marrold/BBCWinchesterPro/images/HDINIT_8BIT.jpg

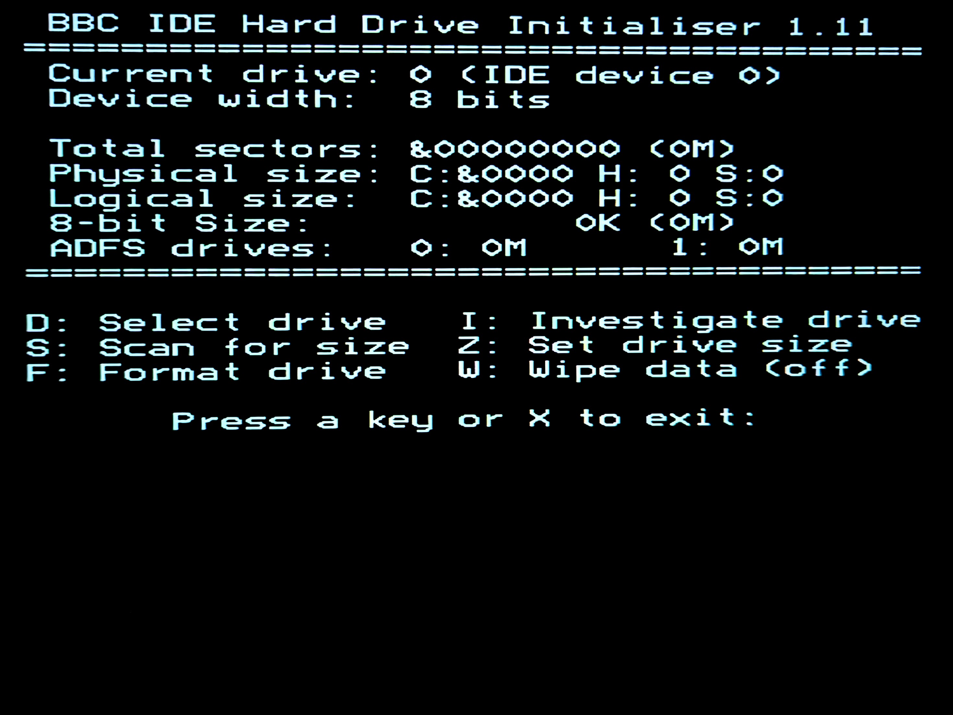
images/HDINIT_8BIT.jpg
