marrold/BBCWinchesterPro/images/HDINIT_FORMAT.jpg

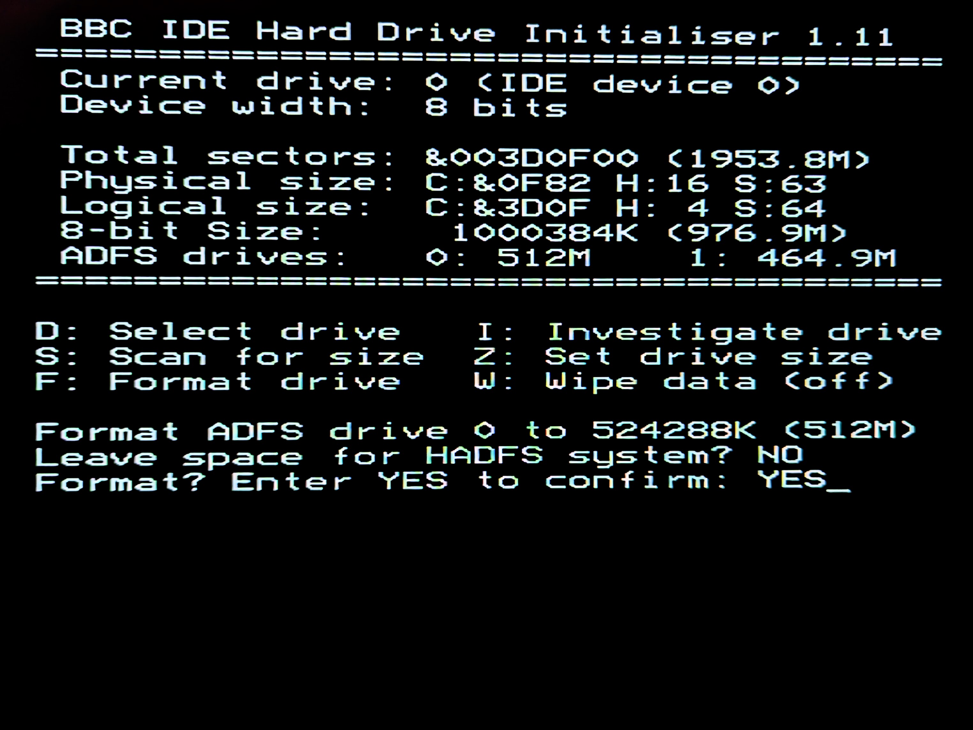
images/HDINIT_FORMAT.jpg
