marrold/BBCWinchesterPro/images/HDINIT_INVESTIGATE.jpg

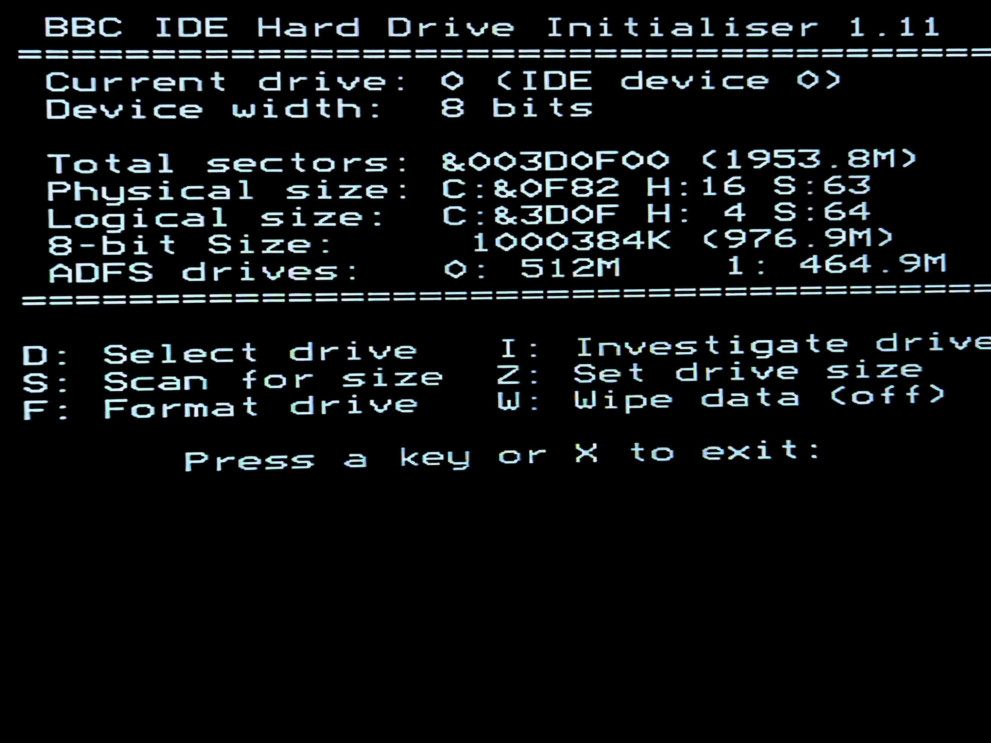
images/HDINIT_INVESTIGATE.jpg
